djacobow/rigminder2/ard/rigwatcher_v2_sdascl/SoftTX.h

/*
Hacked up SoftSerial to remove all Rx (and its interrupt)

*/

#ifndef SoftTX_h
#define SoftTX_h

#include <inttypes.h>
#include <Stream.h>

/******************************************************************************
* Definitions
******************************************************************************/

#ifndef _SS_MAX_RX_BUFF
#define _SS_MAX_RX_BUFF 64 // RX buffer size
#endif

#ifndef GCC_VERSION
#define GCC_VERSION (__GNUC__ * 10000 + __GNUC_MINOR__ * 100 + __GNUC_PATCHLEVEL__)
#endif

class SoftTX : public Stream
{
private:
  // per object data
  uint8_t _transmitBitMask;
  volatile uint8_t *_transmitPortRegister;

  uint16_t _buffer_overflow:1;
  uint16_t _inverse_logic:1;
  uint16_t _tx_delay;
  // static data
  static SoftTX *active_object;

  // private methods
  inline void recv() __attribute__((__always_inline__));
  uint8_t rx_pin_read();
  void setTX(uint8_t transmitPin);
  void setRX(uint8_t receivePin);

  // Return num - sub, or 1 if the result would be < 1
  static uint16_t subtract_cap(uint16_t num, uint16_t sub);

  // private static method for timing
  static inline void tunedDelay(uint16_t delay);

public:
  // public methods
  SoftTX(uint8_t transmitPin, bool inverse_logic = false);
  ~SoftTX();
  void begin(long speed);
  bool listen();
  void end();
  bool isListening() { return this == active_object; }
  bool stopListening();
  bool overflow() { bool ret = _buffer_overflow; if (ret) _buffer_overflow = false; return ret; }
  int peek();

  virtual size_t write(uint8_t byte);
  virtual int read();
  virtual int available();
  virtual void flush();
  operator bool() { return true; }
  
  using Print::write;

  // public only for easy access by interrupt handlers
  static inline void handle_interrupt() __attribute__((__always_inline__));
};

// Arduino 0012 workaround
#undef int
#undef char
#undef long
#undef byte
#undef float
#undef abs
#undef round

#endif
